shreyachillargikar-ctrl/NIRMAAN_AERONEX-25/Software/AI model/Trained_YOLOV8s/BoxF1_curve.png

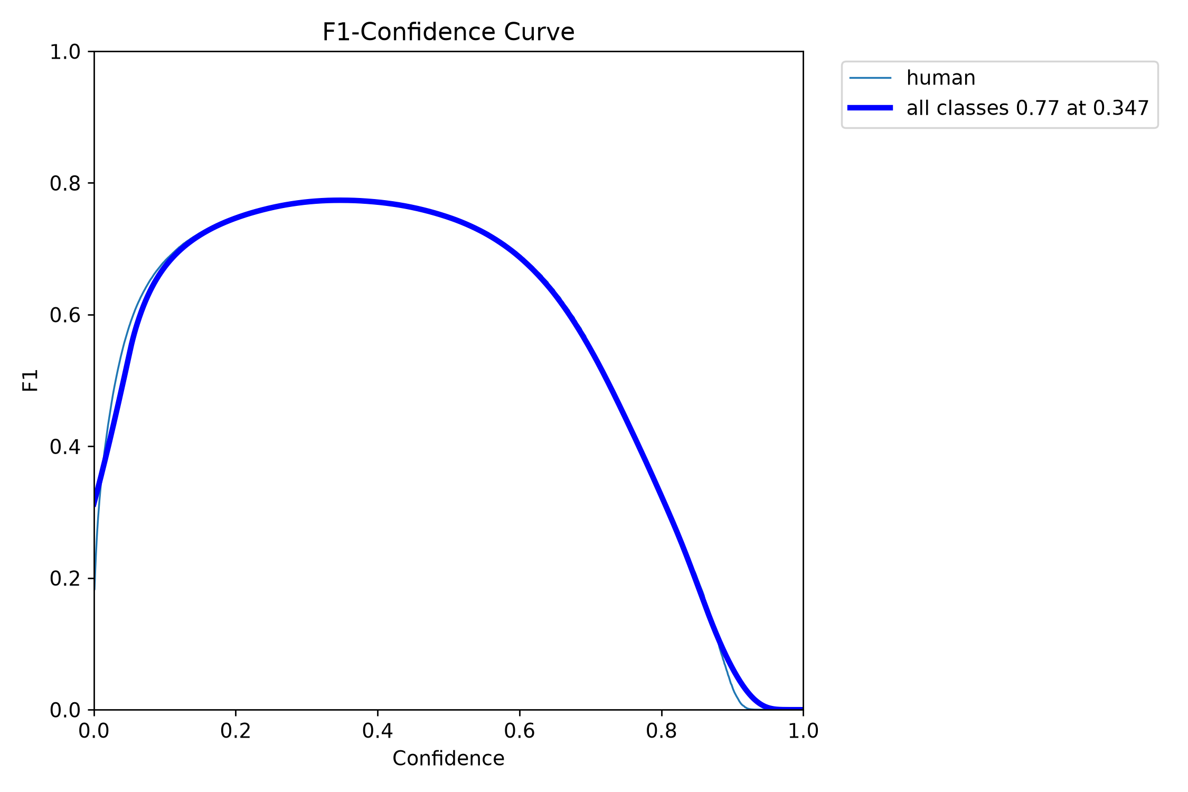
Software/AI model/Trained_YOLOV8s/BoxF1_curve.png
