shreyachillargikar-ctrl/NIRMAAN_AERONEX-25/Software/AI model/Trained_YOLOV8s/confusion_matrix_normalized.png

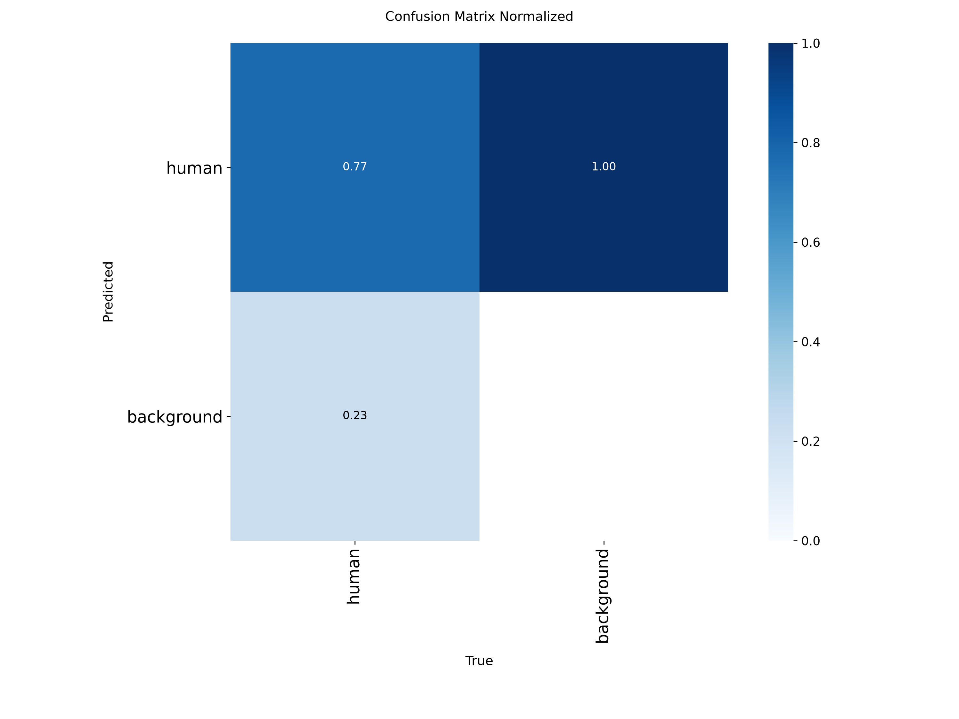
Software/AI model/Trained_YOLOV8s/confusion_matrix_normalized.png
