shreyachillargikar-ctrl/NIRMAAN_AERONEX-25/Software/AI model/Trained_YOLOV8s/train_batch0.jpg

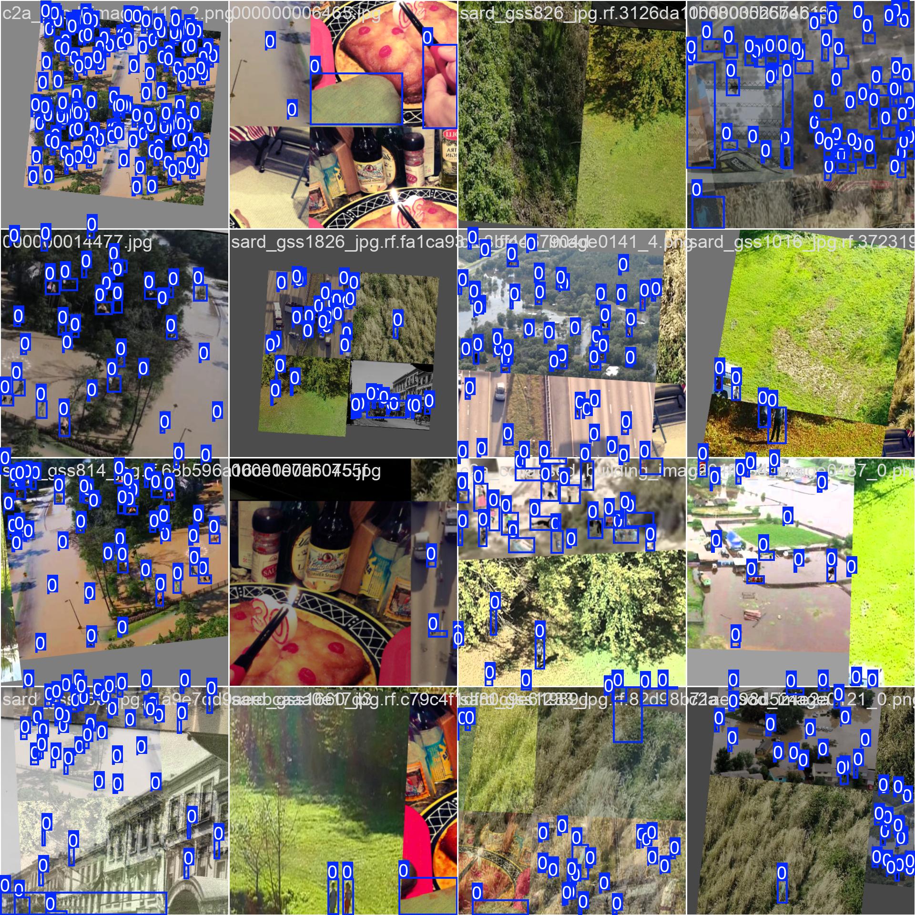
Software/AI model/Trained_YOLOV8s/train_batch0.jpg
