shreyachillargikar-ctrl/NIRMAAN_AERONEX-25/Software/AI model/Trained_YOLOV8s/train_batch2.jpg

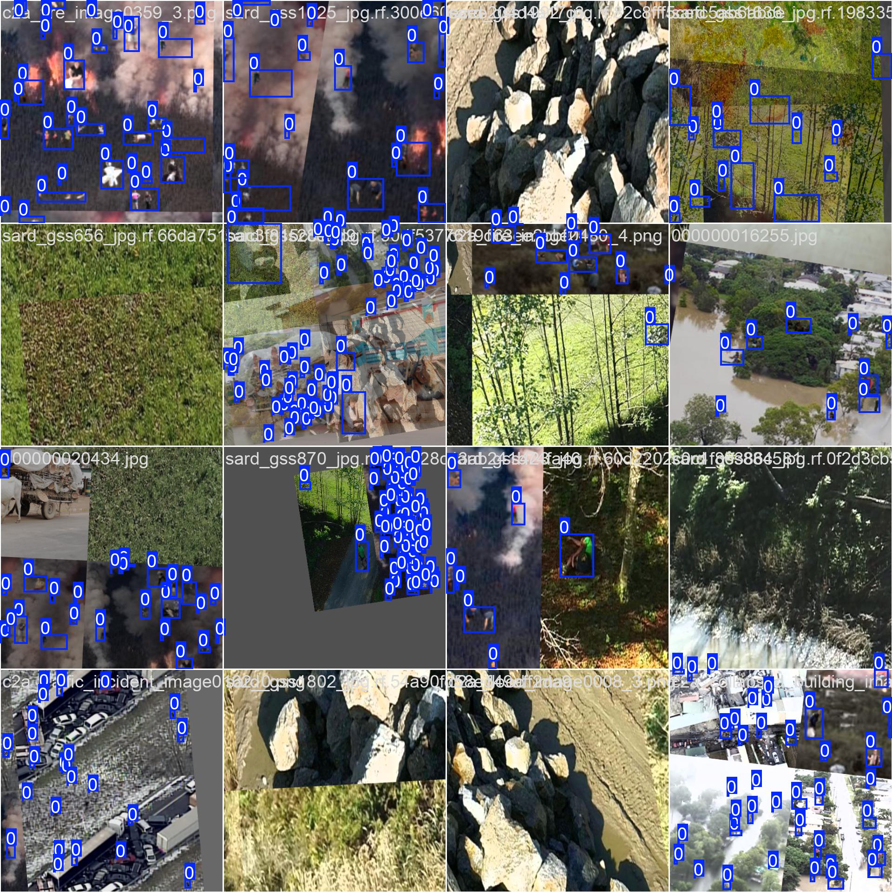
Software/AI model/Trained_YOLOV8s/train_batch2.jpg
