shreyachillargikar-ctrl/NIRMAAN_AERONEX-25/Software/AI model/Trained_YOLOV8s/train_batch37080.jpg

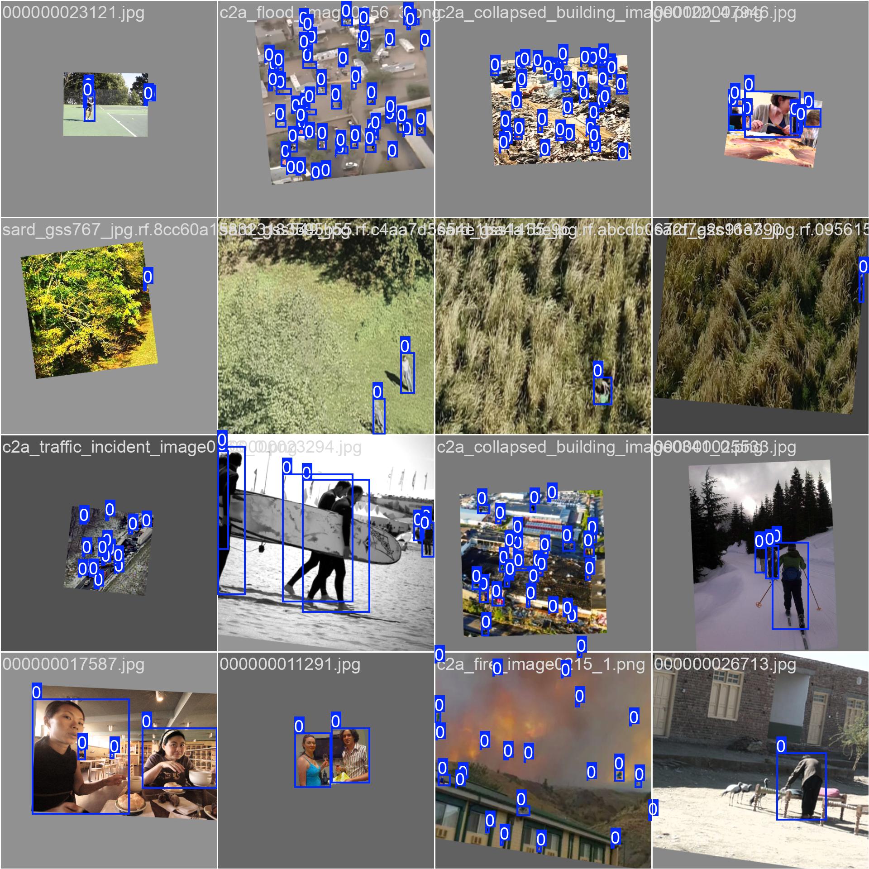
Software/AI model/Trained_YOLOV8s/train_batch37080.jpg
