shreyachillargikar-ctrl/NIRMAAN_AERONEX-25/Software/AI model/Trained_YOLOV8s/train_batch37081.jpg

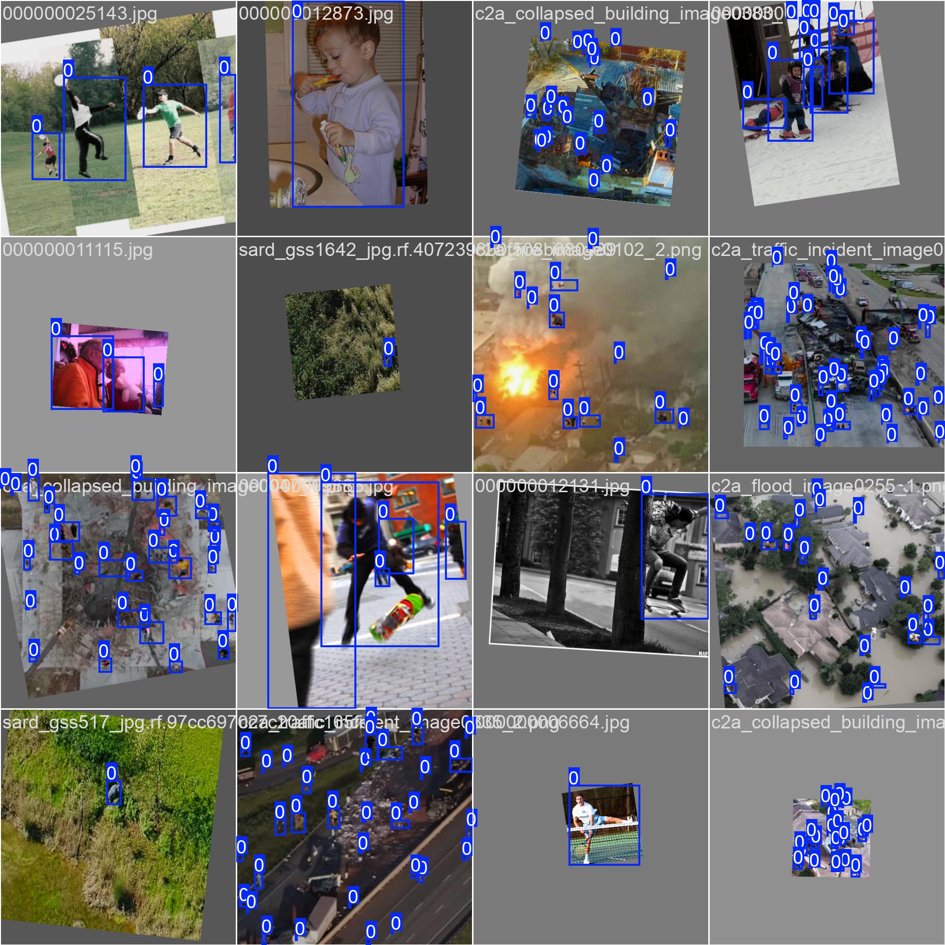
Software/AI model/Trained_YOLOV8s/train_batch37081.jpg
