shreyachillargikar-ctrl/NIRMAAN_AERONEX-25/Software/AI model/Trained_YOLOV8s/val_batch1_labels.jpg

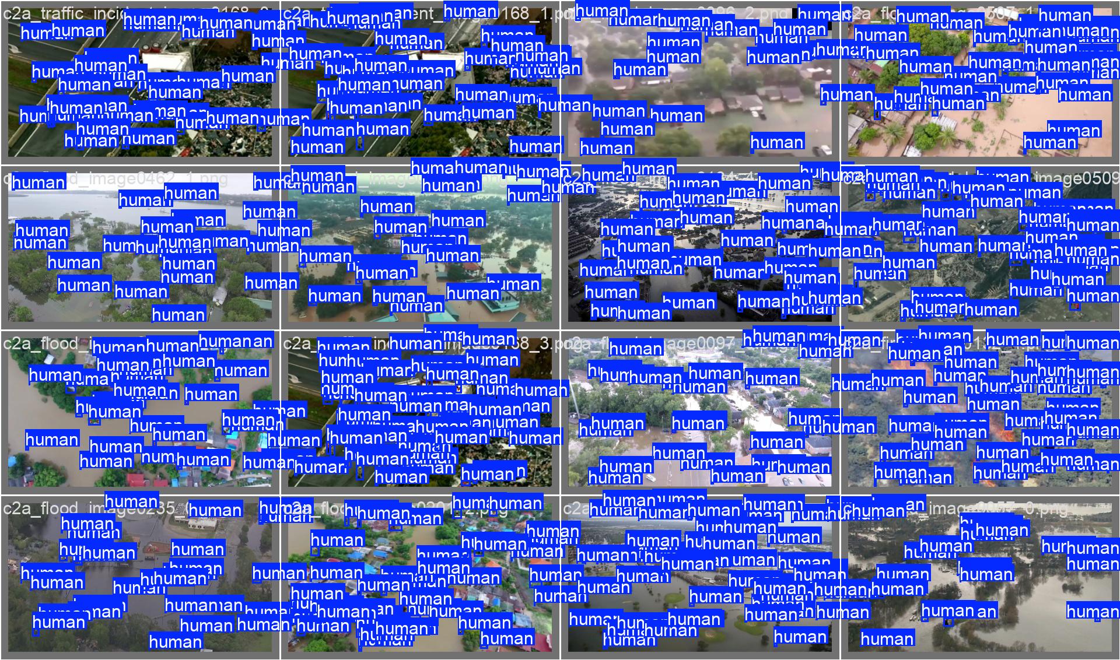
Software/AI model/Trained_YOLOV8s/val_batch1_labels.jpg
